Bertruss/BatteryHealthMonitor/schematic/simulation/sim.asc

input_pin: res; 2000k
R1: res; 500k
R2: res; 500k
R3: res; 760k
R4: res; 500k
R5: res; 2.9R
R6: res; .01R
R7: res; 200k
R8: res; 22
R9: res; 220
U1: UniversalOpAmp1
U2: 7805
U4: UniversalOpAmp1
V2: voltage; 6
Named nets: 0, testout, mid
.dc V2 5 5 .01
