Bertruss/BatteryHealthMonitor/src/bhmDisplay.c

#include "../include/bhmDisplay.h"
#include "../include/SSD1306_driver.h"
#include "../include/fnt.h"
#include "../include/TinyTWI.h"
#include "../include/TinyEeprom.h"
#include "../include/bhmADC.h"

// bhmDisplay is a collection of graphics drawing functions specific to the battery health monitor use case.

// width = 25;
// height = 4;
/*
|	Z |~~~~~~~~~~~~~~~~~| 100%
|	V :  	A : 
|	EST. TIME : ____  	
| 			[warning]
*/

const uint8_t graphics[16] = {
	0xff, 0xff,  // endcap
	0x01, 0x40,  // empty ind
	0xf1, 0x4f,  // full ind
	0x04, 0x01,  // begin - lightning bolt
	0x10, 0x05,
	0x40, 0x11,
	0x00, 0x41	// end - lightning bolt
};

char time_txt[9] = {'E', 'S', 'T', '.', ' ', 'T', 'I', 'M', 'E'}; // might be too ambitious
char warning_txt[25] = {'B', 'A', 'T', 'T', 'E', 'R', 'Y', ' ', 'L','E','V','E','L',' ','C','R','I','T','I','C','A','L', 0};
char voltage_txt[9] = {'V', 'O', 'L', 'T', 'A', 'G', 'E', ':', 0};
char current_txt[9] = {'C', 'U', 'R', 'R', 'E', 'N','T', ':', 0};

void update_display(uint8_t percent, bool warn, uint32_t voltage, uint32_t current){
	draw_percent_bar(percent);
	display_voltage(voltage);
	display_current(current);
	// draw time estimate?
	if(warn){
		display_warning();
	}else{
		clear_warning();
	}
}

void write_char(char val){
	// retrieve address of character bitmap from eeprom
	if(val == ' '){
		render_symbol(255);
	}else{
		render_symbol(characterLookup(val));
	}
}

void render_symbol(uint8_t address){// 
	/* 
	/ this thing is d u m b.
	/ let me explain:
	/ the SSD1306 with 128x32 pixel oled screen technically has screen buffer large enough for a screen twice that size;
	/ the same chip drives a 128x64 oled. So, you might assume (like me), that must mean that only half the addressable buffer is used. 
	/ You would be wrong.
	/ No, instead, for reasons that are murky to me, they decided that it made more sense to map full bytes to nibbles, 
	/ only drawing every other bit to the screen in this form 01010101b. So you either have to waste space pre-encoding your data
	/ to expand every byte to two bytes, or you have to waste cycles splitting every byte into two bytes. leading to the monstrosity below.
	/ admittedly this is compounded by the font needing to be flipped from its orientation in memory, the screen is written LSB first.
	*/
	uint8_t buff;
	uint8_t char_buffer[5] = {0x00,0x00,0x00,0x00,0x00};
	if(address != 255){
		eeprom_read(char_buffer, address, 5);
	}
	uint8_t i = 0;
	uint8_t ii = 0;
	while(i != 0x15){
		ii = (i & 0x0F);
		buff = 
		((char_buffer[ii] & 0x80) >> 7) +
		((char_buffer[ii] & 0x40) >> 4) +
		((char_buffer[ii] & 0x20) >> 1) +
		((char_buffer[ii] & 0x10) << 2);
		char_buffer[ii] = (0x0F & char_buffer[ii]) << 4;
		SSD1306_draw(buff);
		i++;
		if(i == 5){
			i = 0x10;
			SSD1306_set_cursor(cursor_pg+1, cursor_col);
		}
	}
	SSD1306_set_cursor(cursor_pg-1, cursor_col+5);
}

void draw_graphic(uint8_t addr){
	// draw graphic selected from library 
	SSD1306_draw(graphics[addr]);
	SSD1306_set_cursor(cursor_pg+1, cursor_col);
	SSD1306_draw(graphics[addr+1]);
	SSD1306_set_cursor(cursor_pg-1, cursor_col+1);
}

void draw_percent_bar(uint8_t percent){
	// draw percent bar 0-100
	//set cursor
	SSD1306_set_cursor(0, 0);

	//draw lightning bolt
	for(int i = 0; i < 4; i++){
		draw_graphic(2*i+6);
	}
	// add a line
	SSD1306_set_cursor(cursor_pg, ++cursor_col);
	
	//draw the start of the percent bar
	draw_graphic(0);
	draw_graphic(2);
	int i = 0;
	for(; i < 95; i++){
		if(i < percent - 5){
			draw_graphic(4);
		}else{
			draw_graphic(2);
		}
	}
	//draw the endcap
	draw_graphic(0);
	
	// line spacer 
	SSD1306_set_cursor(cursor_pg, ++cursor_col);
	display_percent_charge(percent);	
}

void clear_warning(){
	SSD1306_clear_segment(6, 0, 127);
	SSD1306_clear_segment(7, 0, 127);
}

void display_warning(){
	SSD1306_set_cursor(6, 0);
	for(int i = 0; i < 22 ; i++){
		write_char(warning_txt[i]);		
	}
}

void display_percent_charge(uint8_t value){
	// writes out battery percentage estimate
	value = (value > 100)? 100 : value;
	uint8_t temp = 0;
	// ascii numbers start with address 0x2D in the font
	if(value == 100){
		render_symbol(num_offset + 6);
		SSD1306_set_cursor(cursor_pg, cursor_col-2); //adjusting weird kerning
		render_symbol(num_offset);
		render_symbol(num_offset);
	}else{
		temp = value/10;
		render_symbol(temp*5 + num_offset);
		
		value = value % 10;
		render_symbol(value*5 + num_offset);
	}
	write_char('%');
}

void display_4digit(uint32_t value, char unit){
	// pull up to 4 sig figs, display with decimal point and unit
	
	uint8_t buff[4] = {0x00, 0x00, 0x00, 0x00};
	
	//10's place
	buff[0] = value/(fixed_point*10);
	value = value % (fixed_point*10);
	
	//1's place
	buff[1] = value/fixed_point;
	value = value % fixed_point;
	
	//.1's place
	buff[2] = value/(fixed_point/10);
	value = value % (fixed_point/10);

	// pull the .01's
	buff[3] = value/(fixed_point/100);
	
	if(buff[0] != 0x00){ // 10's place is optional
		render_symbol(num_offset + buff[0]*5);
	}
	render_symbol(num_offset + buff[1]*5);
	write_char('.');
	render_symbol(num_offset + buff[2]*5);
	render_symbol(num_offset + buff[3]*5);
	write_char(unit);
}

void display_voltage(uint32_t value){
	// Put voltage to display
	
	SSD1306_set_cursor(2, 0);
	char* ptr = &voltage_txt;
	do{
		write_char(*ptr);
	}while(*(++ptr) != 0);
	display_4digit(value, 'V');
	display_delete();
}

void display_current(uint32_t value){
	//  display amperage
	
	SSD1306_set_cursor(4, 0);
	char* ptr = &current_txt;
	do{
		write_char(*ptr);
	}while(*(++ptr) != 0);
	
	display_4digit(value, 'A');
	display_delete();
}

void display_delete(){
	//clears current cursor position
	uint8_t len = 5;
	while(len > 0){
		len--;
		SSD1306_draw(0x00);
	}
	SSD1306_offset_cursor(1, 0); //shift down to bottom half of the cursor segment for this font
	len = 5;
	while(len > 0){
		len--;
		SSD1306_draw(0x00);
	}
	SSD1306_reset_cursor();
}
